afiskon/ayn-4b/images/bpfs/17.png

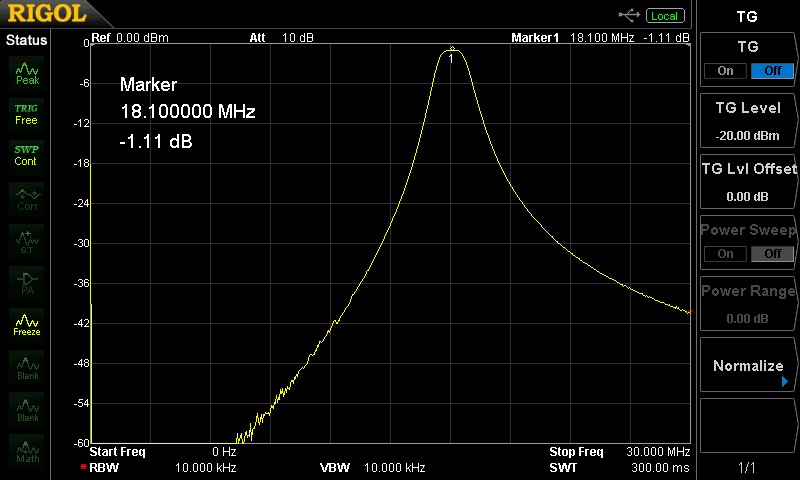
images/bpfs/17.png
