afiskon/ayn-4b/images/bpfs/20.png

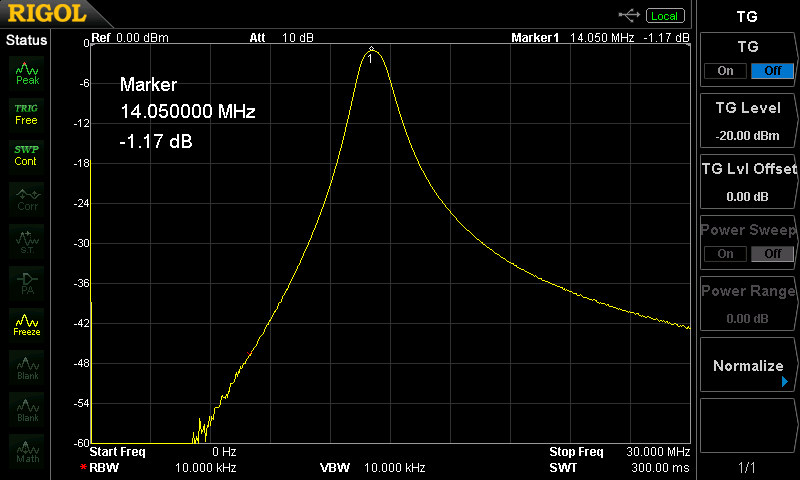
images/bpfs/20.png
