afiskon/ayn-4b/images/bpfs/30.png

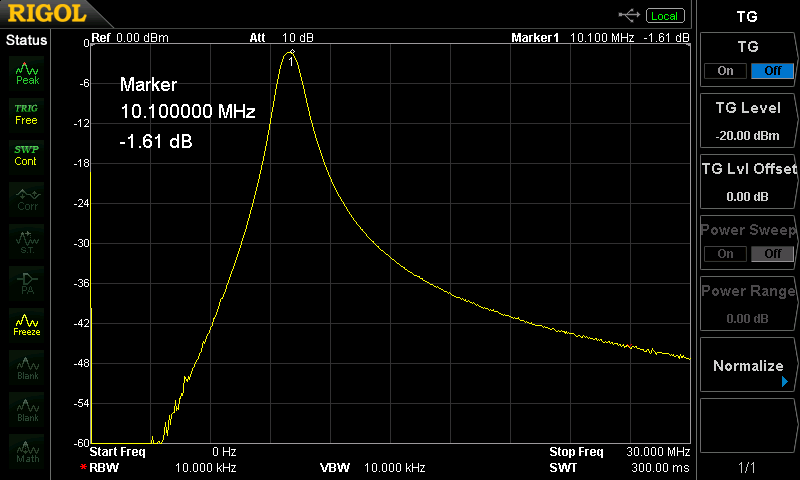
images/bpfs/30.png
