afiskon/ayn-4b/images/bpfs/40.png

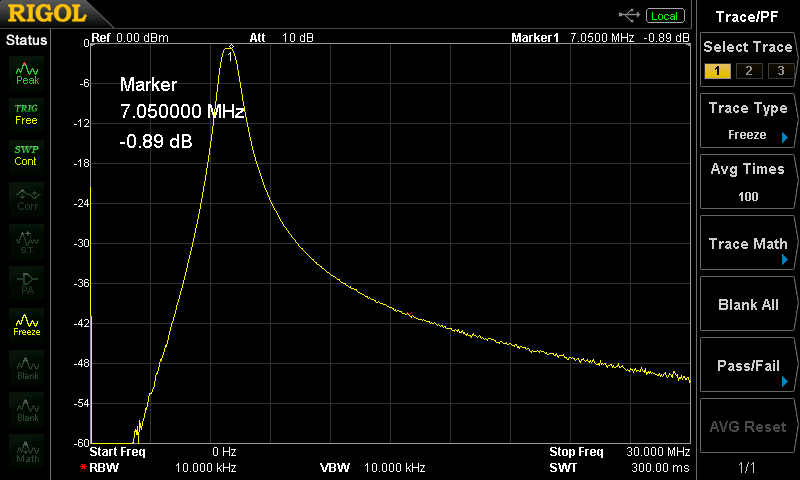
images/bpfs/40.png
