afiskon/ayn-4b/images/lpfs/2017.png

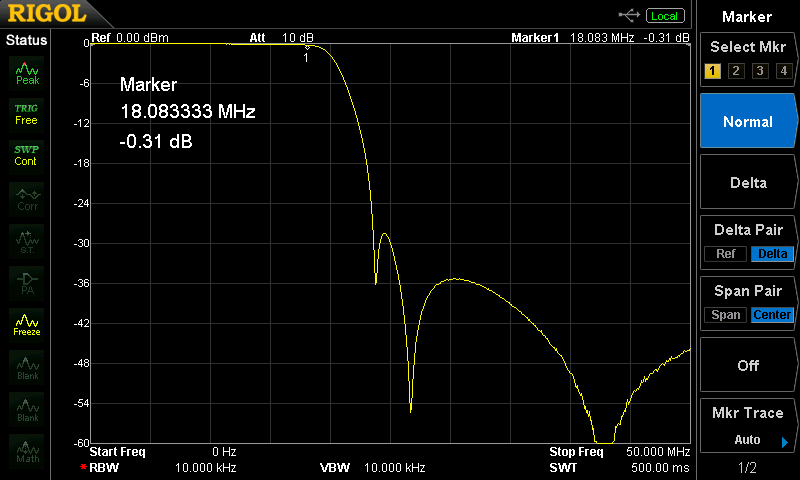
images/lpfs/2017.png
