afiskon/ayn-4b/images/lpfs/4030.png

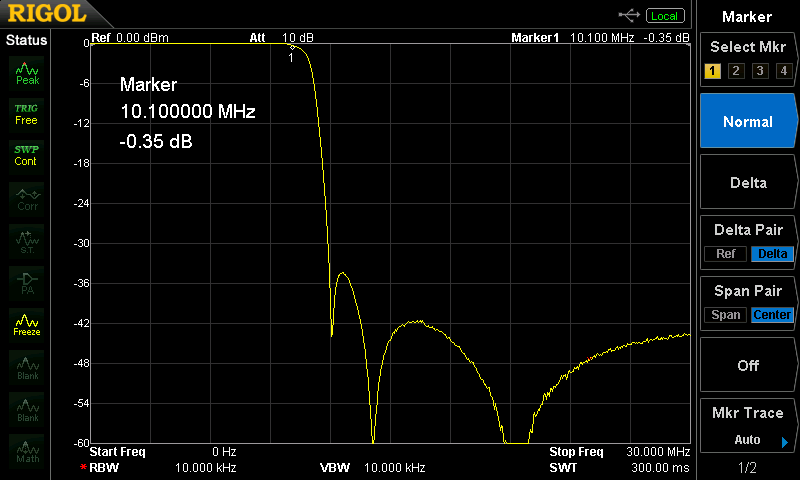
images/lpfs/4030.png
