afiskon/ayn-4b/images/power/17.png

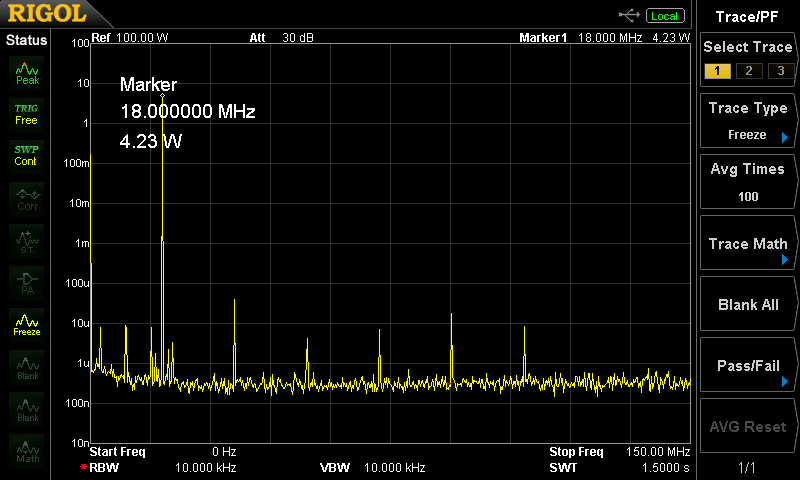
images/power/17.png
