afiskon/ayn-4b/images/power/20.png

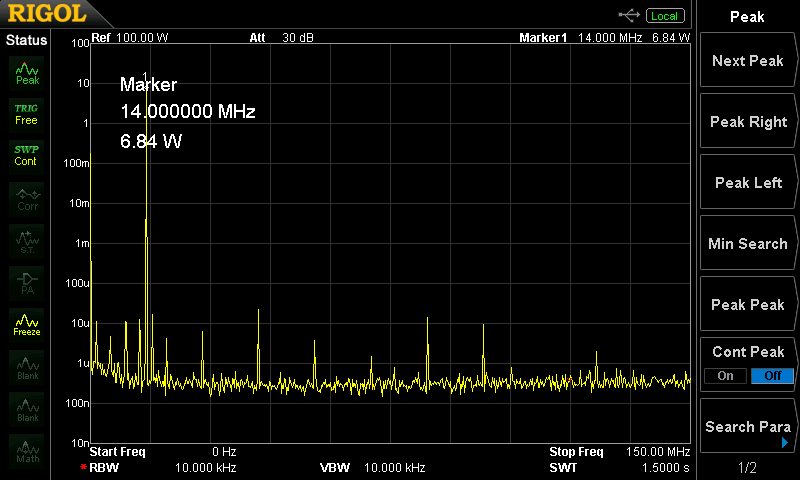
images/power/20.png
