afiskon/ayn-4b/images/power/30.png

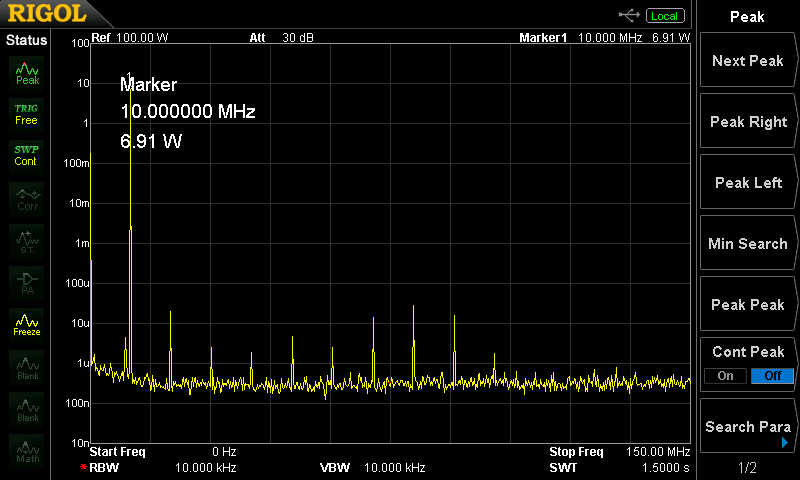
images/power/30.png
