afiskon/ayn-4b/images/xtal-filter/3db-bandwidth.png

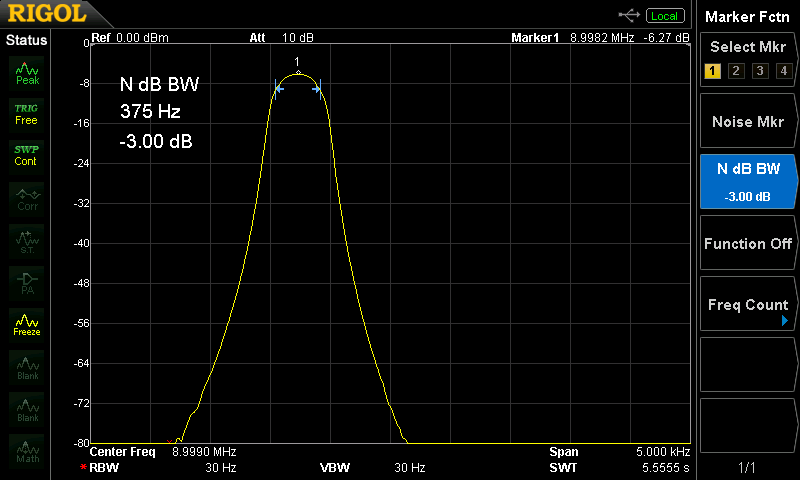
images/xtal-filter/3db-bandwidth.png
